umbacos/PCB_MOD65/pcb/MOD65.kicad_sch

## KiCad design pcb/MOD65.kicad_sch (2025-06-22)

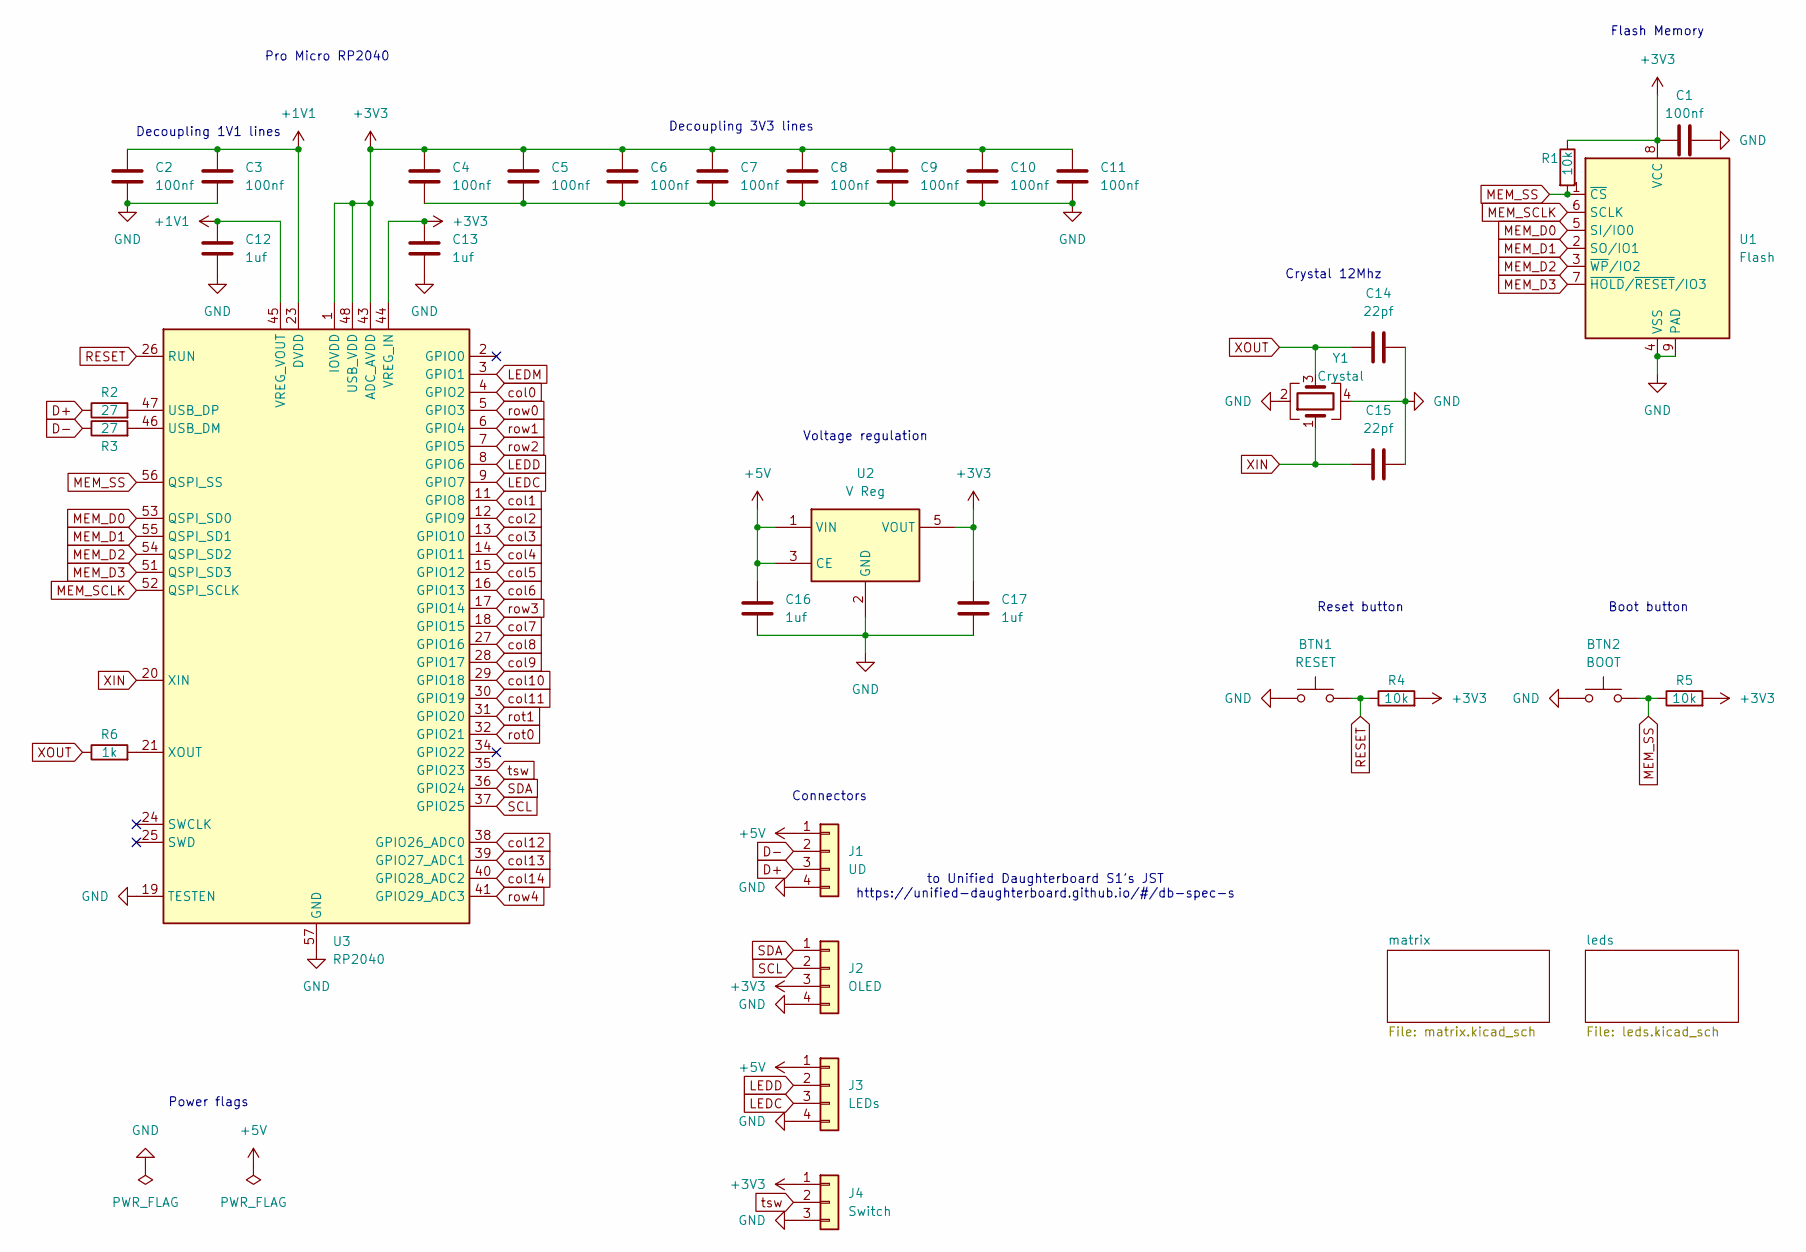
[picture p2: schematic MOD65.kicad_sch]

Parts:
BTN1: RESET; SW_SPST_TL3342; Part Number TL3342F450QG; JLCPCB Part C2886898
BTN2: BOOT; SW_SPST_TL3342; Part Number TL3342F450QG; JLCPCB Part C2886898
C1, C2, C3, C4, C5, C6, C7, C8, C9, C10, C11: 100nf; C_0805_2012Metric; Part Number CL21B104KCFNNNE; JLCPCB Part C28233
C12, C13, C16, C17: 1uf; C_0805_2012Metric; Part Number CL21B105KBFNNNE; JLCPCB Part C28323
C14, C15: 22pf; C_0805_2012Metric; Part Number CL21C220JBANNNC; JLCPCB Part C1804
J1: UD; JST_SH_SM04B-SRSS-TB_1x04-1MP_P1.00mm_Horizontal; Part Number SM04B-SRSS-TB(LF)(SN); JLCPCB Part C160404
J2: OLED; JST_SH_SM04B-SRSS-TB_1x04-1MP_P1.00mm_Horizontal; Part Number SM04B-SRSS-TB(LF)(SN); JLCPCB Part C160404
J3: LEDs; JST_SH_SM04B-SRSS-TB_1x04-1MP_P1.00mm_Horizontal; Part Number SM04B-SRSS-TB(LF)(SN); JLCPCB Part C160404
J4: Switch; JST_SH_SM03B-SRSS-TB_1x03-1MP_P1.00mm_Horizontal; Part Number SM03B-SRSS-TB(LF)(SN); JLCPCB Part C160403
R1, R4, R5: 10k; R_0805_2012Metric; Part Number 0805W8F1002T5E; JLCPCB Part C17414
R2, R3: 27; R_0805_2012Metric; Part Number 0805W8F270JT5E; JLCPCB Part C17594
R6: 1k; R_0805_2012Metric; Part Number 0805W8F1001T5E; JLCPCB Part C17513
U1: Flash; WSON-8-1EP_8x6mm_P1.27mm_EP3.4x4.3mm; Part Number GD25Q256EYIGR; JLCPCB Part C2927043
U2: V Reg; SOT-23-5; Part Number XC6210B332MR; JLCPCB Part C3021084
U3: RP2040; QFN-56-1EP_7x7mm_P0.4mm_EP3.2x3.2mm; Part Number RP2040; JLCPCB Part C2040
Y1: Crystal; Crystal_SMD_3225-4Pin_3.2x2.5mm; Part Number DSX321G 12MHz; JLCPCB Part C93234

Connections:
+1V1: C2.2, C3.2, C12.2, U3.23 (DVDD), U3.45 (VREG_VOUT), U3.50 (DVDD)
+3V3: C1.2, C4.2, C5.2, C6.2, C7.2, C8.2, C9.2, C10.2, C11.2, C13.2, C17.1, J2.3, J4.1, R1.1, R4.2, R5.2, U1.8 (VCC), U2.5 (VOUT), U3.1 (IOVDD), U3.10 (IOVDD), U3.22 (IOVDD), U3.33 (IOVDD), U3.42 (IOVDD), U3.43 (ADC_AVDD), U3.44 (VREG_IN), U3.48 (USB_VDD), U3.49 (IOVDD)
+5V: C16.1, J1.1, J3.1, U2.1 (VIN), U2.3 (CE)
D+: J1.3, R2.1
D-: J1.2, R3.1
GND: BTN1.1, BTN2.1, C1.1, C2.1, C3.1, C4.1, C5.1, C6.1, C7.1, C8.1, C9.1, C10.1, C11.1, C12.1, C13.1, C14.2, C15.2, C16.2, C17.2, J1.4, J2.4, J3.4, J4.3, U1.4 (VSS), U1.9 (PAD), U2.2 (GND), U3.19 (TESTEN), U3.57 (GND), Y1.2, Y1.4
LEDC: J3.3, U3.9 (GPIO7)
LEDD: J3.2, U3.8 (GPIO6)
LEDM: U3.3 (GPIO1)
MEM_D0: U1.5 (SI/IO0), U3.53 (QSPI_SD0)
MEM_D1: U1.2 (SO/IO1), U3.55 (QSPI_SD1)
MEM_D2: U1.3 (~WP/IO2), U3.54 (QSPI_SD2)
MEM_D3: U1.7 (~HOLD/~RESET/IO3), U3.51 (QSPI_SD3)
MEM_SCLK: U1.6 (SCLK), U3.52 (QSPI_SCLK)
MEM_SS: BTN2.2, R1.2, R5.1, U1.1 (~CS), U3.56 (QSPI_SS)
unnamed: R2.2, U3.47 (USB_DP)
unnamed: R3.2, U3.46 (USB_DM)
unnamed: R6.2, U3.21 (XOUT)
RESET: BTN1.2, R4.1, U3.26 (RUN)
SCL: J2.2, U3.37 (GPIO25)
SDA: J2.1, U3.36 (GPIO24)
XIN: C15.1, U3.20 (XIN), Y1.1
XOUT: C14.1, R6.1, Y1.3
col0: U3.4 (GPIO2)
col1: U3.11 (GPIO8)
col2: U3.12 (GPIO9)
col3: U3.13 (GPIO10)
col4: U3.14 (GPIO11)
col5: U3.15 (GPIO12)
col6: U3.16 (GPIO13)
col7: U3.18 (GPIO15)
col8: U3.27 (GPIO16)
col9: U3.28 (GPIO17)
col10: U3.29 (GPIO18)
col11: U3.30 (GPIO19)
col12: U3.38 (GPIO26_ADC0)
col13: U3.39 (GPIO27_ADC1)
col14: U3.40 (GPIO28_ADC2)
rot0: U3.32 (GPIO21)
rot1: U3.31 (GPIO20)
row0: U3.5 (GPIO3)
row1: U3.6 (GPIO4)
row2: U3.7 (GPIO5)
row3: U3.17 (GPIO14)
row4: U3.41 (GPIO29_ADC3)
tsw: J4.2, U3.35 (GPIO23)

Notes on the sheet:
Decoupling 1V1 lines
Pro Micro RP2040
Boot button
Reset button
Crystal 12Mhz
Power flags
Voltage regulation
to Unified Daughterboard S1's JST https://unified-daughterboard.github.io/#/db-spec-s
Connectors
Flash Memory
Decoupling 3V3 lines
