umbacos/PCB_MOD65/pcb/leds.kicad_sch

## KiCad design pcb/leds.kicad_sch (2025-06-29)

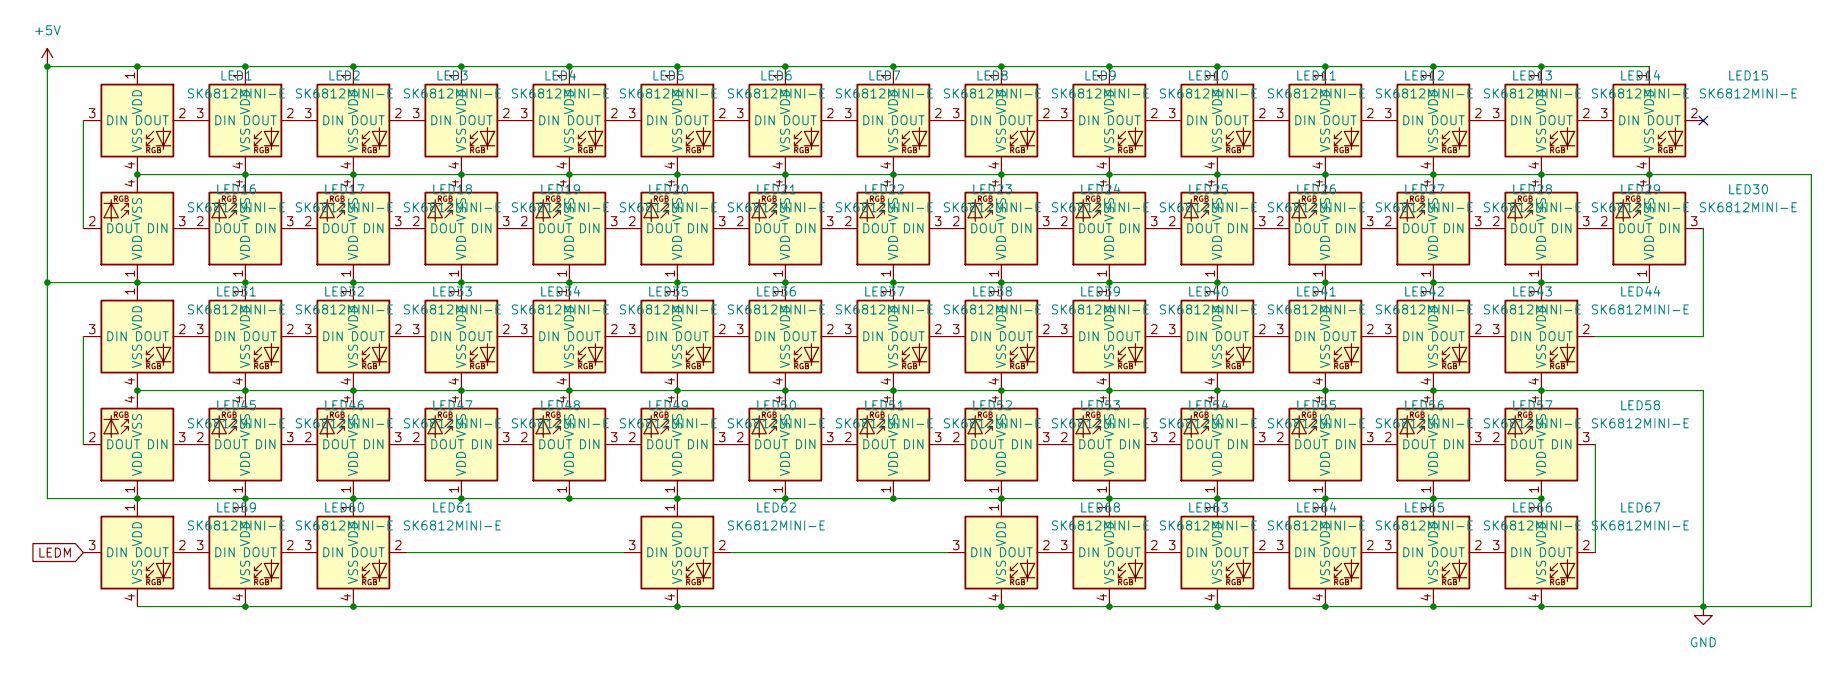
[picture p3: schematic leds.kicad_sch]

Parts:
LED1, LED2, LED3, LED4, LED5, LED6, LED7, LED8, LED9, LED10, LED11, LED12, LED13, LED14, LED15, LED16, LED17, LED18, LED19, LED20, LED21, LED22, LED23, LED24, LED25, LED26, LED27, LED28, LED29, LED30, LED31, LED32, LED33, LED34, LED35, LED36, LED37, LED38, LED39, LED40, LED41, LED42, LED43, LED44, LED45, LED46, LED47, LED48, LED49, LED50, LED51, LED52, LED53, LED54, LED55, LED56, LED57, LED58, LED59, LED60, LED61, LED62, LED63, LED64, LED65, LED66, LED67, LED68: SK6812MINI-E; LED_6028R; Part Number SK6812MINI-E; JLCPCB Part C5149201

Connections:
+5V: LED1.1 (VDD), LED2.1 (VDD), LED3.1 (VDD), LED4.1 (VDD), LED5.1 (VDD), LED6.1 (VDD), LED7.1 (VDD), LED8.1 (VDD), LED9.1 (VDD), LED10.1 (VDD), LED11.1 (VDD), LED12.1 (VDD), LED13.1 (VDD), LED14.1 (VDD), LED15.1 (VDD), LED16.1 (VDD), LED17.1 (VDD), LED18.1 (VDD), LED19.1 (VDD), LED20.1 (VDD), LED21.1 (VDD), LED22.1 (VDD), LED23.1 (VDD), LED24.1 (VDD), LED25.1 (VDD), LED26.1 (VDD), LED27.1 (VDD), LED28.1 (VDD), LED29.1 (VDD), LED30.1 (VDD), LED31.1 (VDD), LED32.1 (VDD), LED33.1 (VDD), LED34.1 (VDD), LED35.1 (VDD), LED36.1 (VDD), LED37.1 (VDD), LED38.1 (VDD), LED39.1 (VDD), LED40.1 (VDD), LED41.1 (VDD), LED42.1 (VDD), LED43.1 (VDD), LED44.1 (VDD), LED45.1 (VDD), LED46.1 (VDD), LED47.1 (VDD), LED48.1 (VDD), LED49.1 (VDD), LED50.1 (VDD), LED51.1 (VDD), LED52.1 (VDD), LED53.1 (VDD), LED54.1 (VDD), LED55.1 (VDD), LED56.1 (VDD), LED57.1 (VDD), LED58.1 (VDD), LED59.1 (VDD), LED60.1 (VDD), LED61.1 (VDD), LED62.1 (VDD), LED63.1 (VDD), LED64.1 (VDD), LED65.1 (VDD), LED66.1 (VDD), LED67.1 (VDD), LED68.1 (VDD)
GND: LED1.4 (VSS), LED2.4 (VSS), LED3.4 (VSS), LED4.4 (VSS), LED5.4 (VSS), LED6.4 (VSS), LED7.4 (VSS), LED8.4 (VSS), LED9.4 (VSS), LED10.4 (VSS), LED11.4 (VSS), LED12.4 (VSS), LED13.4 (VSS), LED14.4 (VSS), LED15.4 (VSS), LED16.4 (VSS), LED17.4 (VSS), LED18.4 (VSS), LED19.4 (VSS), LED20.4 (VSS), LED21.4 (VSS), LED22.4 (VSS), LED23.4 (VSS), LED24.4 (VSS), LED25.4 (VSS), LED26.4 (VSS), LED27.4 (VSS), LED28.4 (VSS), LED29.4 (VSS), LED30.4 (VSS), LED31.4 (VSS), LED32.4 (VSS), LED33.4 (VSS), LED34.4 (VSS), LED35.4 (VSS), LED36.4 (VSS), LED37.4 (VSS), LED38.4 (VSS), LED39.4 (VSS), LED40.4 (VSS), LED41.4 (VSS), LED42.4 (VSS), LED43.4 (VSS), LED44.4 (VSS), LED45.4 (VSS), LED46.4 (VSS), LED47.4 (VSS), LED48.4 (VSS), LED49.4 (VSS), LED50.4 (VSS), LED51.4 (VSS), LED52.4 (VSS), LED53.4 (VSS), LED54.4 (VSS), LED55.4 (VSS), LED56.4 (VSS), LED57.4 (VSS), LED58.4 (VSS), LED59.4 (VSS), LED60.4 (VSS), LED61.4 (VSS), LED62.4 (VSS), LED63.4 (VSS), LED64.4 (VSS), LED65.4 (VSS), LED66.4 (VSS), LED67.4 (VSS), LED68.4 (VSS)
LEDM: LED59.3 (DIN)
unnamed: LED1.2 (DOUT), LED2.3 (DIN)
unnamed: LED1.3 (DIN), LED16.2 (DOUT)
unnamed: LED2.2 (DOUT), LED3.3 (DIN)
unnamed: LED3.2 (DOUT), LED4.3 (DIN)
unnamed: LED4.2 (DOUT), LED5.3 (DIN)
unnamed: LED5.2 (DOUT), LED6.3 (DIN)
unnamed: LED6.2 (DOUT), LED7.3 (DIN)
unnamed: LED7.2 (DOUT), LED8.3 (DIN)
unnamed: LED8.2 (DOUT), LED9.3 (DIN)
unnamed: LED10.2 (DOUT), LED11.3 (DIN)
unnamed: LED9.2 (DOUT), LED10.3 (DIN)
unnamed: LED11.2 (DOUT), LED12.3 (DIN)
unnamed: LED12.2 (DOUT), LED13.3 (DIN)
unnamed: LED13.2 (DOUT), LED14.3 (DIN)
unnamed: LED14.2 (DOUT), LED15.3 (DIN)
unnamed: LED16.3 (DIN), LED17.2 (DOUT)
unnamed: LED17.3 (DIN), LED18.2 (DOUT)
unnamed: LED18.3 (DIN), LED19.2 (DOUT)
unnamed: LED19.3 (DIN), LED20.2 (DOUT)
unnamed: LED20.3 (DIN), LED21.2 (DOUT)
unnamed: LED21.3 (DIN), LED22.2 (DOUT)
unnamed: LED22.3 (DIN), LED23.2 (DOUT)
unnamed: LED23.3 (DIN), LED24.2 (DOUT)
unnamed: LED24.3 (DIN), LED25.2 (DOUT)
unnamed: LED25.3 (DIN), LED26.2 (DOUT)
unnamed: LED26.3 (DIN), LED27.2 (DOUT)
unnamed: LED27.3 (DIN), LED28.2 (DOUT)
unnamed: LED28.3 (DIN), LED29.2 (DOUT)
unnamed: LED29.3 (DIN), LED30.2 (DOUT)
unnamed: LED30.3 (DIN), LED44.2 (DOUT)
unnamed: LED31.2 (DOUT), LED32.3 (DIN)
unnamed: LED31.3 (DIN), LED45.2 (DOUT)
unnamed: LED32.2 (DOUT), LED33.3 (DIN)
unnamed: LED33.2 (DOUT), LED34.3 (DIN)
unnamed: LED34.2 (DOUT), LED35.3 (DIN)
unnamed: LED35.2 (DOUT), LED36.3 (DIN)
unnamed: LED36.2 (DOUT), LED37.3 (DIN)
unnamed: LED37.2 (DOUT), LED38.3 (DIN)
unnamed: LED38.2 (DOUT), LED39.3 (DIN)
unnamed: LED39.2 (DOUT), LED40.3 (DIN)
unnamed: LED40.2 (DOUT), LED41.3 (DIN)
unnamed: LED41.2 (DOUT), LED42.3 (DIN)
unnamed: LED42.2 (DOUT), LED43.3 (DIN)
unnamed: LED43.2 (DOUT), LED44.3 (DIN)
unnamed: LED45.3 (DIN), LED46.2 (DOUT)
unnamed: LED46.3 (DIN), LED47.2 (DOUT)
unnamed: LED47.3 (DIN), LED48.2 (DOUT)
unnamed: LED48.3 (DIN), LED49.2 (DOUT)
unnamed: LED49.3 (DIN), LED50.2 (DOUT)
unnamed: LED50.3 (DIN), LED51.2 (DOUT)
unnamed: LED51.3 (DIN), LED52.2 (DOUT)
unnamed: LED52.3 (DIN), LED53.2 (DOUT)
unnamed: LED53.3 (DIN), LED54.2 (DOUT)
unnamed: LED54.3 (DIN), LED55.2 (DOUT)
unnamed: LED55.3 (DIN), LED56.2 (DOUT)
unnamed: LED56.3 (DIN), LED57.2 (DOUT)
unnamed: LED57.3 (DIN), LED58.2 (DOUT)
unnamed: LED58.3 (DIN), LED67.2 (DOUT)
unnamed: LED59.2 (DOUT), LED60.3 (DIN)
unnamed: LED60.2 (DOUT), LED61.3 (DIN)
unnamed: LED61.2 (DOUT), LED62.3 (DIN)
unnamed: LED62.2 (DOUT), LED68.3 (DIN)
unnamed: LED63.2 (DOUT), LED64.3 (DIN)
unnamed: LED63.3 (DIN), LED68.2 (DOUT)
unnamed: LED64.2 (DOUT), LED65.3 (DIN)
unnamed: LED65.2 (DOUT), LED66.3 (DIN)
unnamed: LED66.2 (DOUT), LED67.3 (DIN)
