umbacos/PCB_MOD65/pcb/matrix.kicad_sch

## KiCad design pcb/matrix.kicad_sch (2025-06-29)

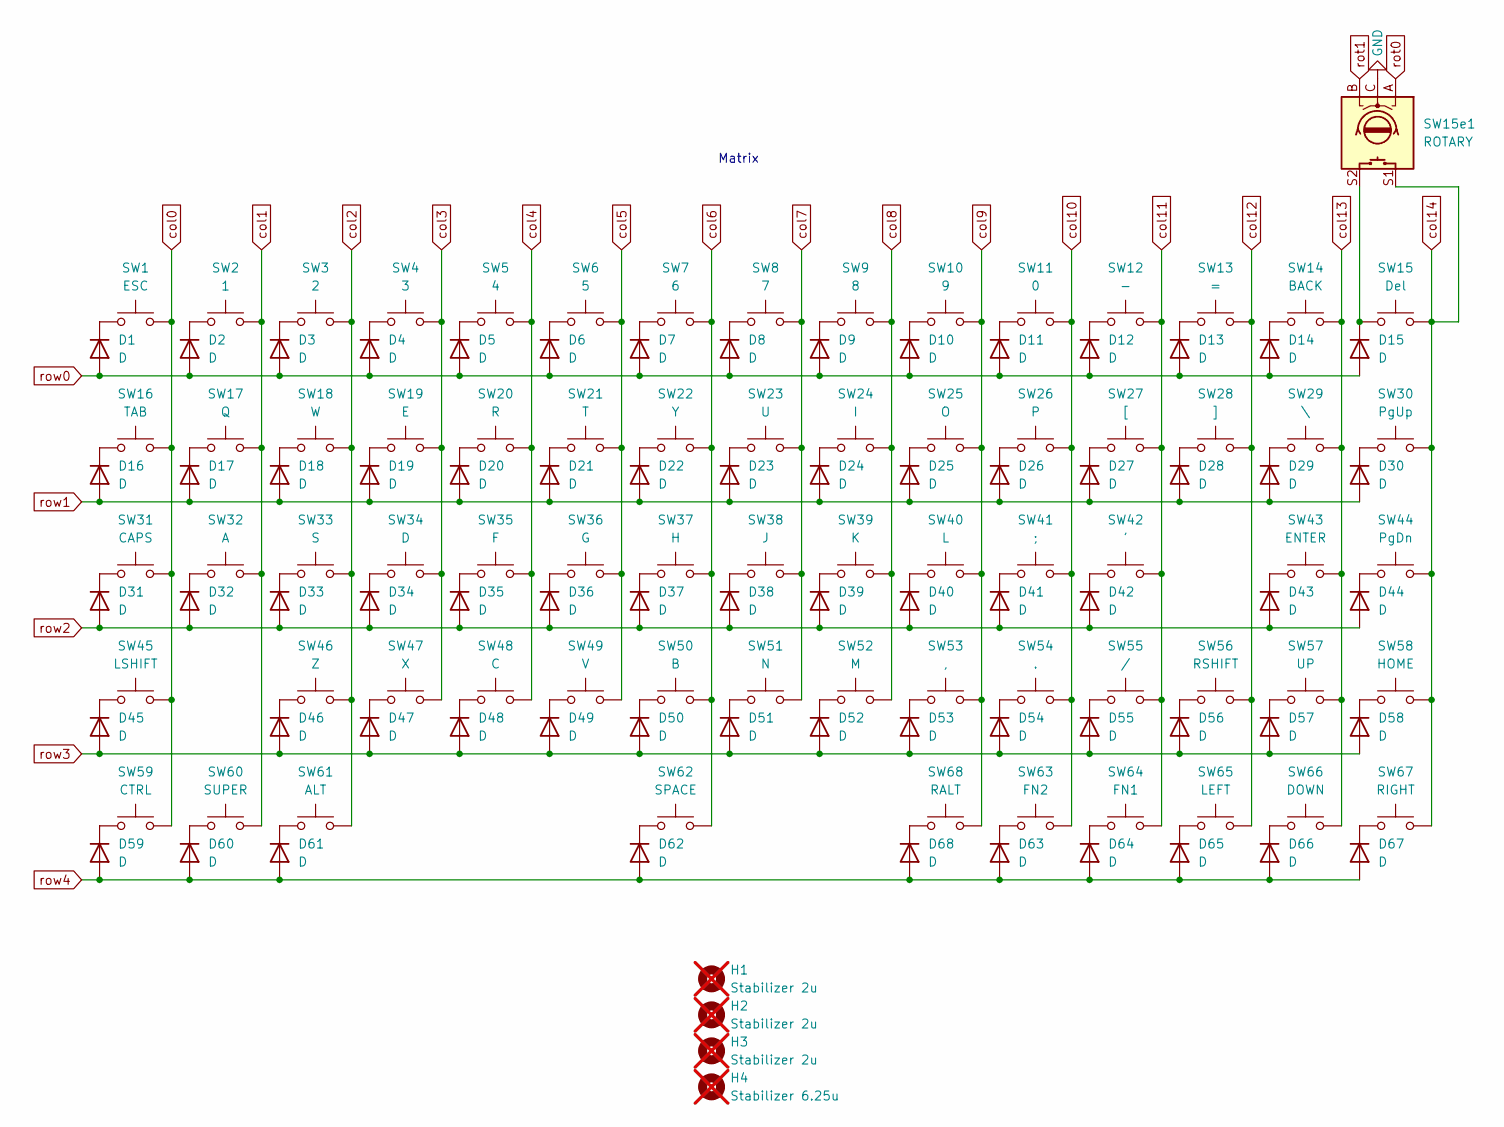
[picture p4: schematic matrix.kicad_sch]

Parts:
D1, D2, D3, D4, D5, D6, D7, D8, D9, D10, D11, D12, D13, D14, D15, D16, D17, D18, D19, D20, D21, D22, D23, D24, D25, D26, D27, D28, D29, D30, D31, D32, D33, D34, D35, D36, D37, D38, D39, D40, D41, D42, D43, D44, D45, D46, D47, D48, D49, D50, D51, D52, D53, D54, D55, D56, D57, D58, D59, D60, D61, D62, D63, D64, D65, D66, D67, D68: D; D_SOD-323; Part Number 1N4148WS; JLCPCB Part C2128
H1, H2, H3: Stabilizer 2u; STAB_MX_2u; not fitted
H4: Stabilizer 6.25u; STAB_MX_6.25u; not fitted
SW1: ESC; SW_MX_HS_CPG151101S11_1u; Part Number CPG151101S11-16; JLCPCB Part C41430893
SW2: 1; SW_MX_HS_CPG151101S11_1u; Part Number CPG151101S11-16; JLCPCB Part C41430893
SW3: 2; SW_MX_HS_CPG151101S11_1u; Part Number CPG151101S11-16; JLCPCB Part C41430893
SW4: 3; SW_MX_HS_CPG151101S11_1u; Part Number CPG151101S11-16; JLCPCB Part C41430893
SW5: 4; SW_MX_HS_CPG151101S11_1u; Part Number CPG151101S11-16; JLCPCB Part C41430893
SW6: 5; SW_MX_HS_CPG151101S11_1u; Part Number CPG151101S11-16; JLCPCB Part C41430893
SW7: 6; SW_MX_HS_CPG151101S11_1u; Part Number CPG151101S11-16; JLCPCB Part C41430893
SW8: 7; SW_MX_HS_CPG151101S11_1u; Part Number CPG151101S11-16; JLCPCB Part C41430893
SW9: 8; SW_MX_HS_CPG151101S11_1u; Part Number CPG151101S11-16; JLCPCB Part C41430893
SW10: 9; SW_MX_HS_CPG151101S11_1u; Part Number CPG151101S11-16; JLCPCB Part C41430893
SW11: 0; SW_MX_HS_CPG151101S11_1u; Part Number CPG151101S11-16; JLCPCB Part C41430893
SW12: -; SW_MX_HS_CPG151101S11_1u; Part Number CPG151101S11-16; JLCPCB Part C41430893
SW13: =; SW_MX_HS_CPG151101S11_1u; Part Number CPG151101S11-16; JLCPCB Part C41430893
SW14: BACK; SW_MX_HS_CPG151101S11_1u; Part Number CPG151101S11-16; JLCPCB Part C41430893
SW15: Del; SW_MX_HS_CPG151101S11_1u; Part Number CPG151101S11-16; JLCPCB Part C41430893
SW15e1: ROTARY; ROT_Alps_EC11E-Switch
SW16: TAB; SW_MX_HS_CPG151101S11_1u; Part Number CPG151101S11-16; JLCPCB Part C41430893
SW17: Q; SW_MX_HS_CPG151101S11_1u; Part Number CPG151101S11-16; JLCPCB Part C41430893
SW18: W; SW_MX_HS_CPG151101S11_1u; Part Number CPG151101S11-16; JLCPCB Part C41430893
SW19: E; SW_MX_HS_CPG151101S11_1u; Part Number CPG151101S11-16; JLCPCB Part C41430893
SW20: R; SW_MX_HS_CPG151101S11_1u; Part Number CPG151101S11-16; JLCPCB Part C41430893
SW21: T; SW_MX_HS_CPG151101S11_1u; Part Number CPG151101S11-16; JLCPCB Part C41430893
SW22: Y; SW_MX_HS_CPG151101S11_1u; Part Number CPG151101S11-16; JLCPCB Part C41430893
SW23: U; SW_MX_HS_CPG151101S11_1u; Part Number CPG151101S11-16; JLCPCB Part C41430893
SW24: I; SW_MX_HS_CPG151101S11_1u; Part Number CPG151101S11-16; JLCPCB Part C41430893
SW25: O; SW_MX_HS_CPG151101S11_1u; Part Number CPG151101S11-16; JLCPCB Part C41430893
SW26: P; SW_MX_HS_CPG151101S11_1u; Part Number CPG151101S11-16; JLCPCB Part C41430893
SW27: [; SW_MX_HS_CPG151101S11_1u; Part Number CPG151101S11-16; JLCPCB Part C41430893
SW28: ]; SW_MX_HS_CPG151101S11_1u; Part Number CPG151101S11-16; JLCPCB Part C41430893
SW29: \; SW_MX_HS_CPG151101S11_1u; Part Number CPG151101S11-16; JLCPCB Part C41430893
SW30: PgUp; SW_MX_HS_CPG151101S11_1u; Part Number CPG151101S11-16; JLCPCB Part C41430893
SW31: CAPS; SW_MX_HS_CPG151101S11_1u; Part Number CPG151101S11-16; JLCPCB Part C41430893
SW32: A; SW_MX_HS_CPG151101S11_1u; Part Number CPG151101S11-16; JLCPCB Part C41430893
SW33: S; SW_MX_HS_CPG151101S11_1u; Part Number CPG151101S11-16; JLCPCB Part C41430893
SW34: D; SW_MX_HS_CPG151101S11_1u; Part Number CPG151101S11-16; JLCPCB Part C41430893
SW35: F; SW_MX_HS_CPG151101S11_1u; Part Number CPG151101S11-16; JLCPCB Part C41430893
SW36: G; SW_MX_HS_CPG151101S11_1u; Part Number CPG151101S11-16; JLCPCB Part C41430893
SW37: H; SW_MX_HS_CPG151101S11_1u; Part Number CPG151101S11-16; JLCPCB Part C41430893
SW38: J; SW_MX_HS_CPG151101S11_1u; Part Number CPG151101S11-16; JLCPCB Part C41430893
SW39: K; SW_MX_HS_CPG151101S11_1u; Part Number CPG151101S11-16; JLCPCB Part C41430893
SW40: L; SW_MX_HS_CPG151101S11_1u; Part Number CPG151101S11-16; JLCPCB Part C41430893
SW41: ;; SW_MX_HS_CPG151101S11_1u; Part Number CPG151101S11-16; JLCPCB Part C41430893
SW42: '; SW_MX_HS_CPG151101S11_1u; Part Number CPG151101S11-16; JLCPCB Part C41430893
SW43: ENTER; SW_MX_HS_CPG151101S11_1u; Part Number CPG151101S11-16; JLCPCB Part C41430893
SW44: PgDn; SW_MX_HS_CPG151101S11_1u; Part Number CPG151101S11-16; JLCPCB Part C41430893
SW45: LSHIFT; SW_MX_HS_CPG151101S11_1u; Part Number CPG151101S11-16; JLCPCB Part C41430893
SW46: Z; SW_MX_HS_CPG151101S11_1u; Part Number CPG151101S11-16; JLCPCB Part C41430893
SW47: X; SW_MX_HS_CPG151101S11_1u; Part Number CPG151101S11-16; JLCPCB Part C41430893
SW48: C; SW_MX_HS_CPG151101S11_1u; Part Number CPG151101S11-16; JLCPCB Part C41430893
SW49: V; SW_MX_HS_CPG151101S11_1u; Part Number CPG151101S11-16; JLCPCB Part C41430893
SW50: B; SW_MX_HS_CPG151101S11_1u; Part Number CPG151101S11-16; JLCPCB Part C41430893
SW51: N; SW_MX_HS_CPG151101S11_1u; Part Number CPG151101S11-16; JLCPCB Part C41430893
SW52: M; SW_MX_HS_CPG151101S11_1u; Part Number CPG151101S11-16; JLCPCB Part C41430893
SW53: ,; SW_MX_HS_CPG151101S11_1u; Part Number CPG151101S11-16; JLCPCB Part C41430893
SW54: .; SW_MX_HS_CPG151101S11_1u; Part Number CPG151101S11-16; JLCPCB Part C41430893
SW55: /; SW_MX_HS_CPG151101S11_1u; Part Number CPG151101S11-16; JLCPCB Part C41430893
SW56: RSHIFT; SW_MX_HS_CPG151101S11_1u; Part Number CPG151101S11-16; JLCPCB Part C41430893
SW57: UP; SW_MX_HS_CPG151101S11_1u; Part Number CPG151101S11-16; JLCPCB Part C41430893
SW58: HOME; SW_MX_HS_CPG151101S11_1u; Part Number CPG151101S11-16; JLCPCB Part C41430893
SW59: CTRL; SW_MX_HS_CPG151101S11_1u; Part Number CPG151101S11-16; JLCPCB Part C41430893
SW60: SUPER; SW_MX_HS_CPG151101S11_1u; Part Number CPG151101S11-16; JLCPCB Part C41430893
SW61: ALT; SW_MX_HS_CPG151101S11_1u; Part Number CPG151101S11-16; JLCPCB Part C41430893
SW62: SPACE; SW_MX_HS_CPG151101S11_1u; Part Number CPG151101S11-16; JLCPCB Part C41430893
SW63: FN2; SW_MX_HS_CPG151101S11_1u; Part Number CPG151101S11-16; JLCPCB Part C41430893
SW64: FN1; SW_MX_HS_CPG151101S11_1u; Part Number CPG151101S11-16; JLCPCB Part C41430893
SW65: LEFT; SW_MX_HS_CPG151101S11_1u; Part Number CPG151101S11-16; JLCPCB Part C41430893
SW66: DOWN; SW_MX_HS_CPG151101S11_1u; Part Number CPG151101S11-16; JLCPCB Part C41430893
SW67: RIGHT; SW_MX_HS_CPG151101S11_1u; Part Number CPG151101S11-16; JLCPCB Part C41430893
SW68: RALT; SW_MX_HS_CPG151101S11_1u; Part Number CPG151101S11-16; JLCPCB Part C41430893

Connections:
GND: SW15e1.C
unnamed: D1.1 (K), SW1.1
unnamed: D2.1 (K), SW2.1
unnamed: D3.1 (K), SW3.1
unnamed: D4.1 (K), SW4.1
unnamed: D5.1 (K), SW5.1
unnamed: D6.1 (K), SW6.1
unnamed: D7.1 (K), SW7.1
unnamed: D8.1 (K), SW8.1
unnamed: D9.1 (K), SW9.1
unnamed: D10.1 (K), SW10.1
unnamed: D11.1 (K), SW11.1
unnamed: D12.1 (K), SW12.1
unnamed: D13.1 (K), SW13.1
unnamed: D14.1 (K), SW14.1
unnamed: D15.1 (K), SW15.1, SW15e1.S2
unnamed: D16.1 (K), SW16.1
unnamed: D17.1 (K), SW17.1
unnamed: D18.1 (K), SW18.1
unnamed: D19.1 (K), SW19.1
unnamed: D20.1 (K), SW20.1
unnamed: D21.1 (K), SW21.1
unnamed: D22.1 (K), SW22.1
unnamed: D23.1 (K), SW23.1
unnamed: D24.1 (K), SW24.1
unnamed: D25.1 (K), SW25.1
unnamed: D26.1 (K), SW26.1
unnamed: D27.1 (K), SW27.1
unnamed: D28.1 (K), SW28.1
unnamed: D29.1 (K), SW29.1
unnamed: D30.1 (K), SW30.1
unnamed: D31.1 (K), SW31.1
unnamed: D32.1 (K), SW32.1
unnamed: D33.1 (K), SW33.1
unnamed: D34.1 (K), SW34.1
unnamed: D35.1 (K), SW35.1
unnamed: D36.1 (K), SW36.1
unnamed: D37.1 (K), SW37.1
unnamed: D38.1 (K), SW38.1
unnamed: D39.1 (K), SW39.1
unnamed: D40.1 (K), SW40.1
unnamed: D41.1 (K), SW41.1
unnamed: D42.1 (K), SW42.1
unnamed: D43.1 (K), SW43.1
unnamed: D44.1 (K), SW44.1
unnamed: D45.1 (K), SW45.1
unnamed: D46.1 (K), SW46.1
unnamed: D47.1 (K), SW47.1
unnamed: D48.1 (K), SW48.1
unnamed: D49.1 (K), SW49.1
unnamed: D50.1 (K), SW50.1
unnamed: D51.1 (K), SW51.1
unnamed: D52.1 (K), SW52.1
unnamed: D53.1 (K), SW53.1
unnamed: D54.1 (K), SW54.1
unnamed: D55.1 (K), SW55.1
unnamed: D56.1 (K), SW56.1
unnamed: D57.1 (K), SW57.1
unnamed: D58.1 (K), SW58.1
unnamed: D59.1 (K), SW59.1
unnamed: D60.1 (K), SW60.1
unnamed: D61.1 (K), SW61.1
unnamed: D62.1 (K), SW62.1
unnamed: D63.1 (K), SW63.1
unnamed: D64.1 (K), SW64.1
unnamed: D65.1 (K), SW65.1
unnamed: D66.1 (K), SW66.1
unnamed: D67.1 (K), SW67.1
unnamed: D68.1 (K), SW68.1
col0: SW1.2, SW16.2, SW31.2, SW45.2, SW59.2
col1: SW2.2, SW17.2, SW32.2, SW60.2
col2: SW3.2, SW18.2, SW33.2, SW46.2, SW61.2
col3: SW4.2, SW19.2, SW34.2, SW47.2
col4: SW5.2, SW20.2, SW35.2, SW48.2
col5: SW6.2, SW21.2, SW36.2, SW49.2
col6: SW7.2, SW22.2, SW37.2, SW50.2, SW62.2
col7: SW8.2, SW23.2, SW38.2, SW51.2
col8: SW9.2, SW24.2, SW39.2, SW52.2
col9: SW10.2, SW25.2, SW40.2, SW53.2, SW68.2
col10: SW11.2, SW26.2, SW41.2, SW54.2, SW63.2
col11: SW12.2, SW27.2, SW42.2, SW55.2, SW64.2
col12: SW13.2, SW28.2, SW56.2, SW65.2
col13: SW14.2, SW29.2, SW43.2, SW57.2, SW66.2
col14: SW15.2, SW15e1.S1, SW30.2, SW44.2, SW58.2, SW67.2
rot0: SW15e1.A
rot1: SW15e1.B
row0: D1.2 (A), D2.2 (A), D3.2 (A), D4.2 (A), D5.2 (A), D6.2 (A), D7.2 (A), D8.2 (A), D9.2 (A), D10.2 (A), D11.2 (A), D12.2 (A), D13.2 (A), D14.2 (A), D15.2 (A)
row1: D16.2 (A), D17.2 (A), D18.2 (A), D19.2 (A), D20.2 (A), D21.2 (A), D22.2 (A), D23.2 (A), D24.2 (A), D25.2 (A), D26.2 (A), D27.2 (A), D28.2 (A), D29.2 (A), D30.2 (A)
row2: D31.2 (A), D32.2 (A), D33.2 (A), D34.2 (A), D35.2 (A), D36.2 (A), D37.2 (A), D38.2 (A), D39.2 (A), D40.2 (A), D41.2 (A), D42.2 (A), D43.2 (A), D44.2 (A)
row3: D45.2 (A), D46.2 (A), D47.2 (A), D48.2 (A), D49.2 (A), D50.2 (A), D51.2 (A), D52.2 (A), D53.2 (A), D54.2 (A), D55.2 (A), D56.2 (A), D57.2 (A), D58.2 (A)
row4: D59.2 (A), D60.2 (A), D61.2 (A), D62.2 (A), D63.2 (A), D64.2 (A), D65.2 (A), D66.2 (A), D67.2 (A), D68.2 (A)

Notes on the sheet:
Matrix
